nasaslvt/project-owl/doc/failure-analysis/5V_transient.png

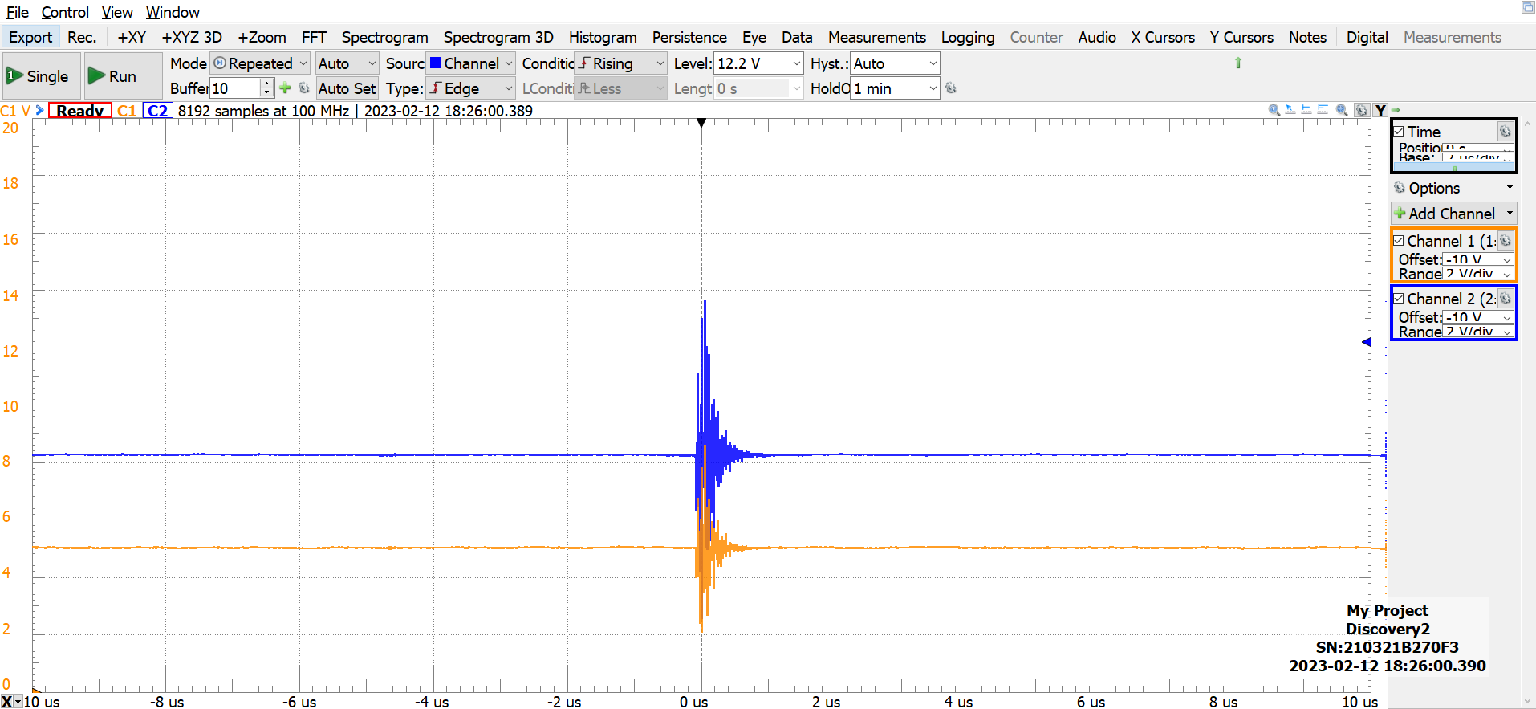
doc/failure-analysis/5V_transient.png
