nasaslvt/project-owl/doc/failure-analysis/Ground_bounce.png

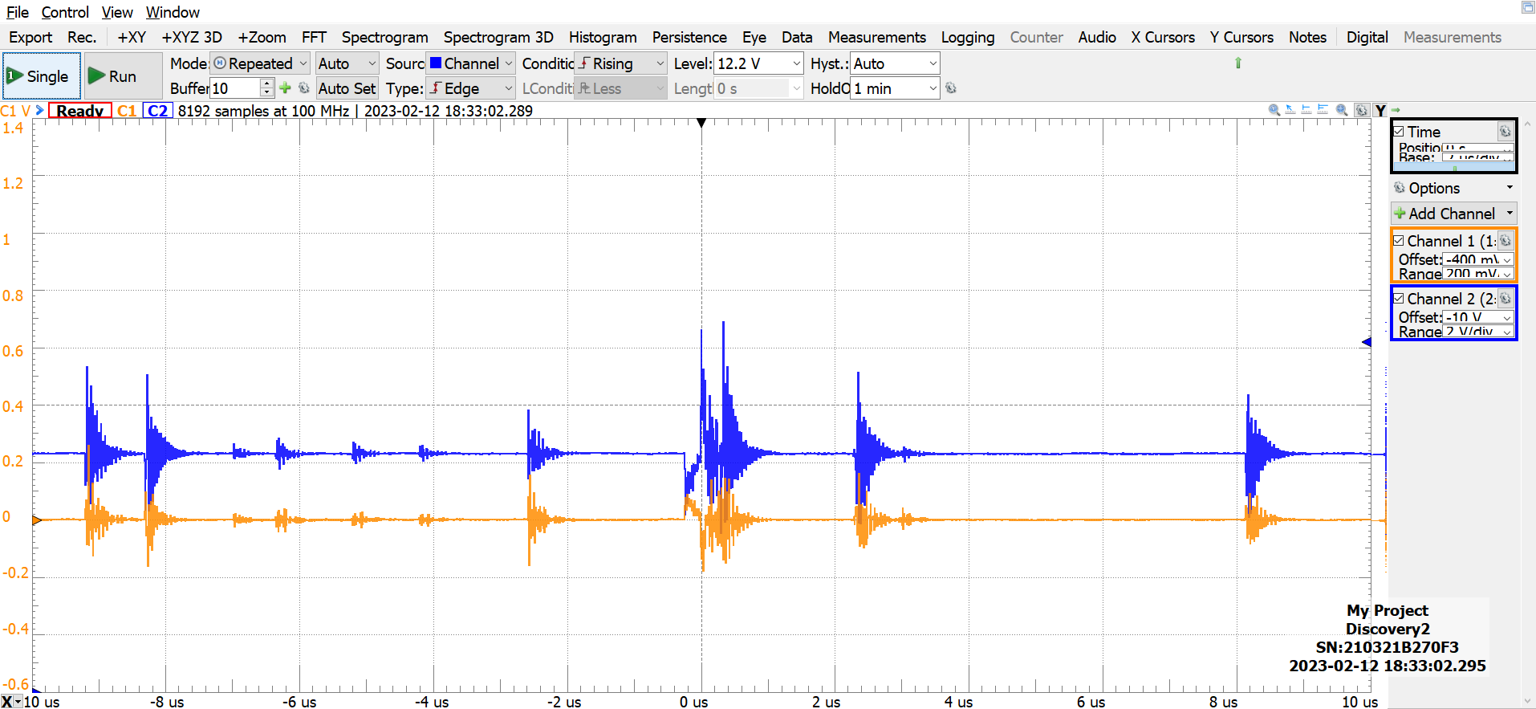
doc/failure-analysis/Ground_bounce.png
