nasaslvt/project-owl/doc/failure-analysis/PWM_kickback.png

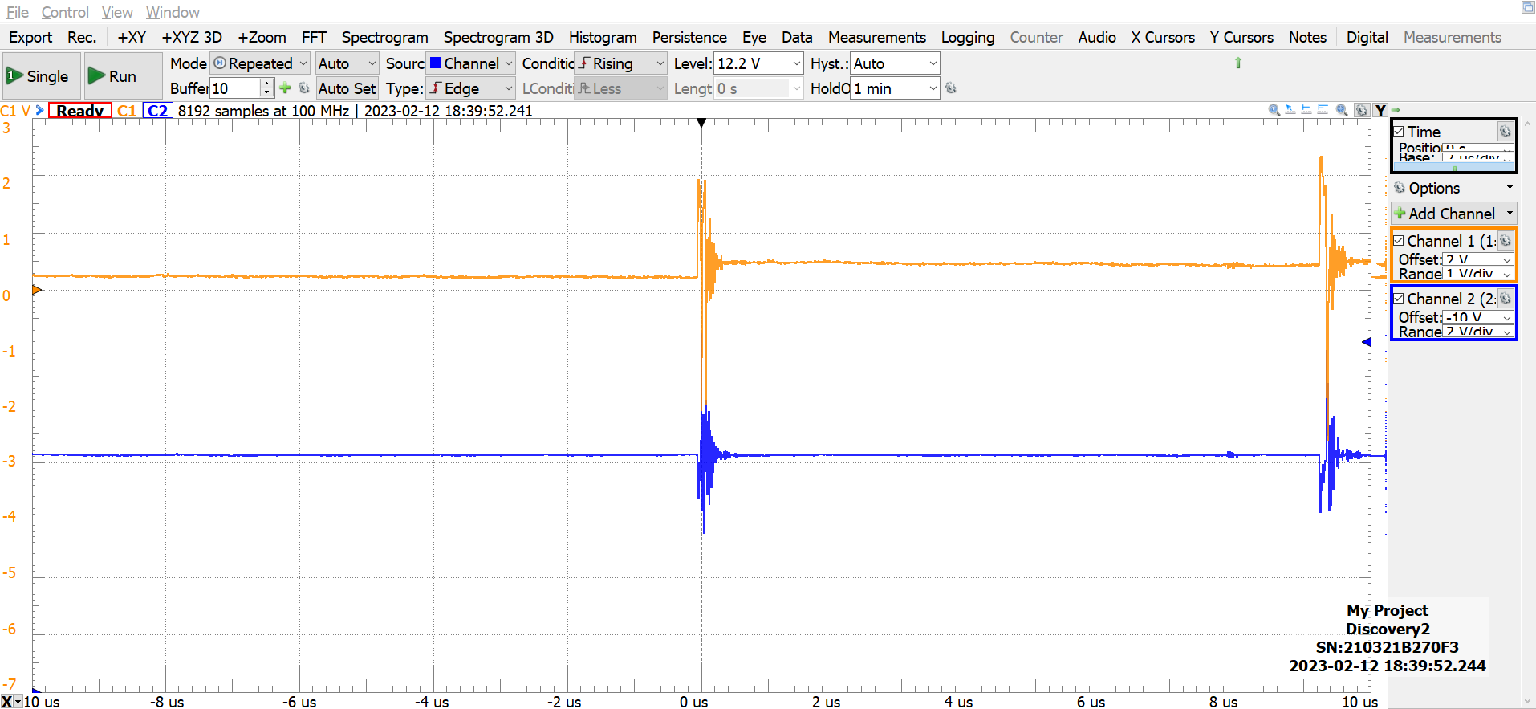
doc/failure-analysis/PWM_kickback.png
