nasaslvt/project-owl/doc/failure-analysis/Servo_startup.png

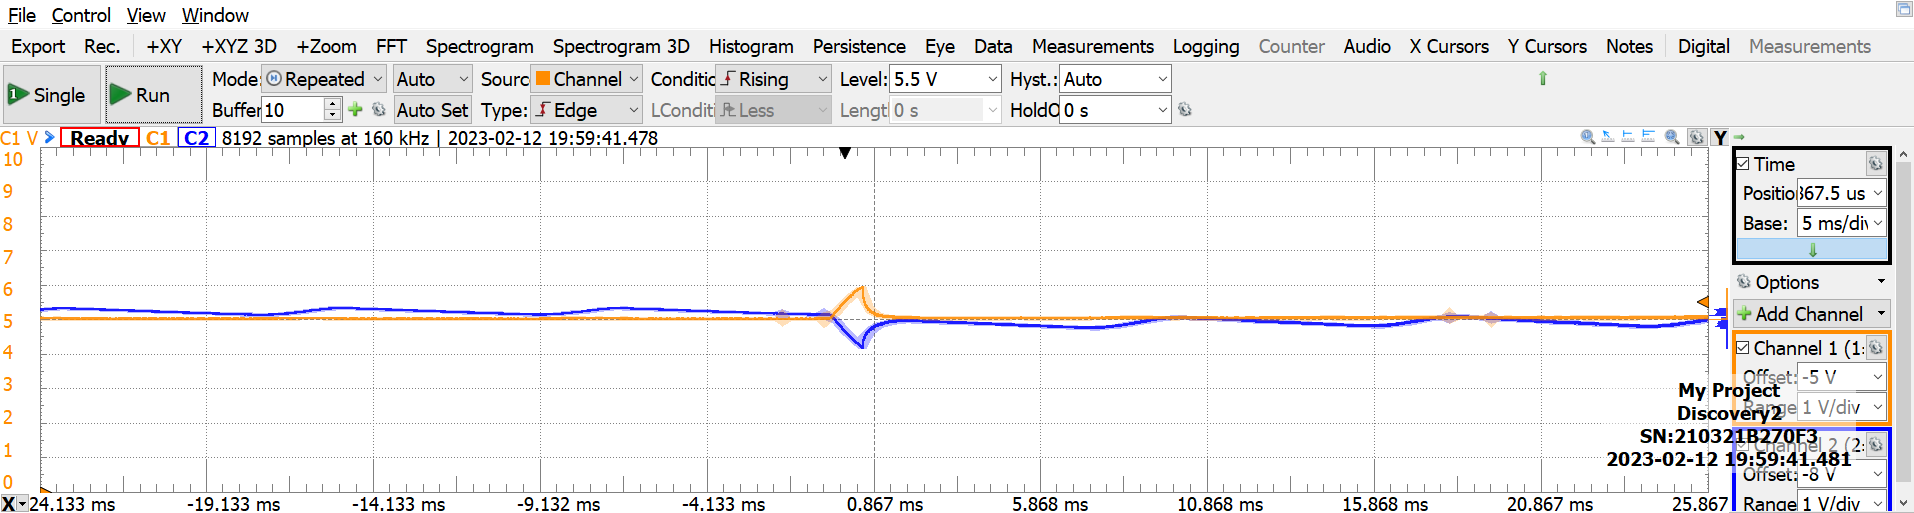
doc/failure-analysis/Servo_startup.png
