nasaslvt/project-owl/doc/Old/cape_route_v1-2.pdf

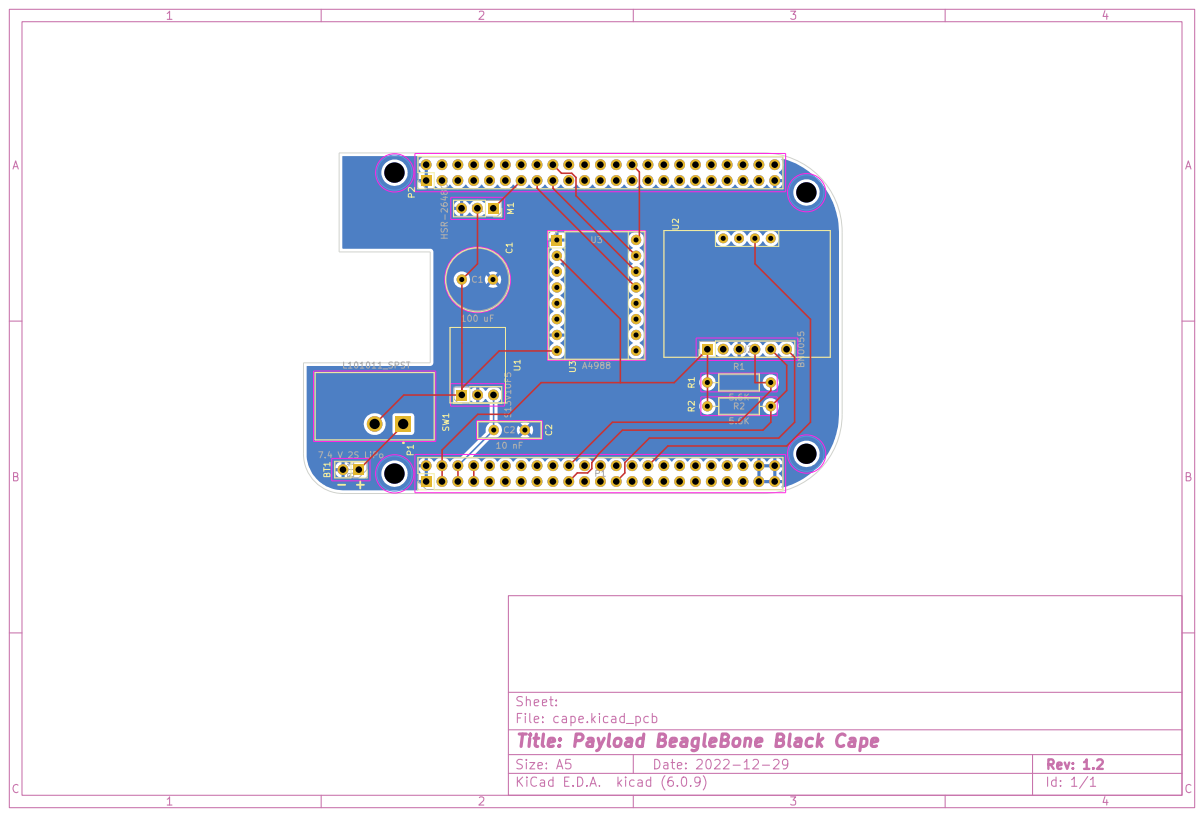
[picture p22: page 1]
