nasaslvt/project-owl/doc/Old/cape_route_v1-1.pdf

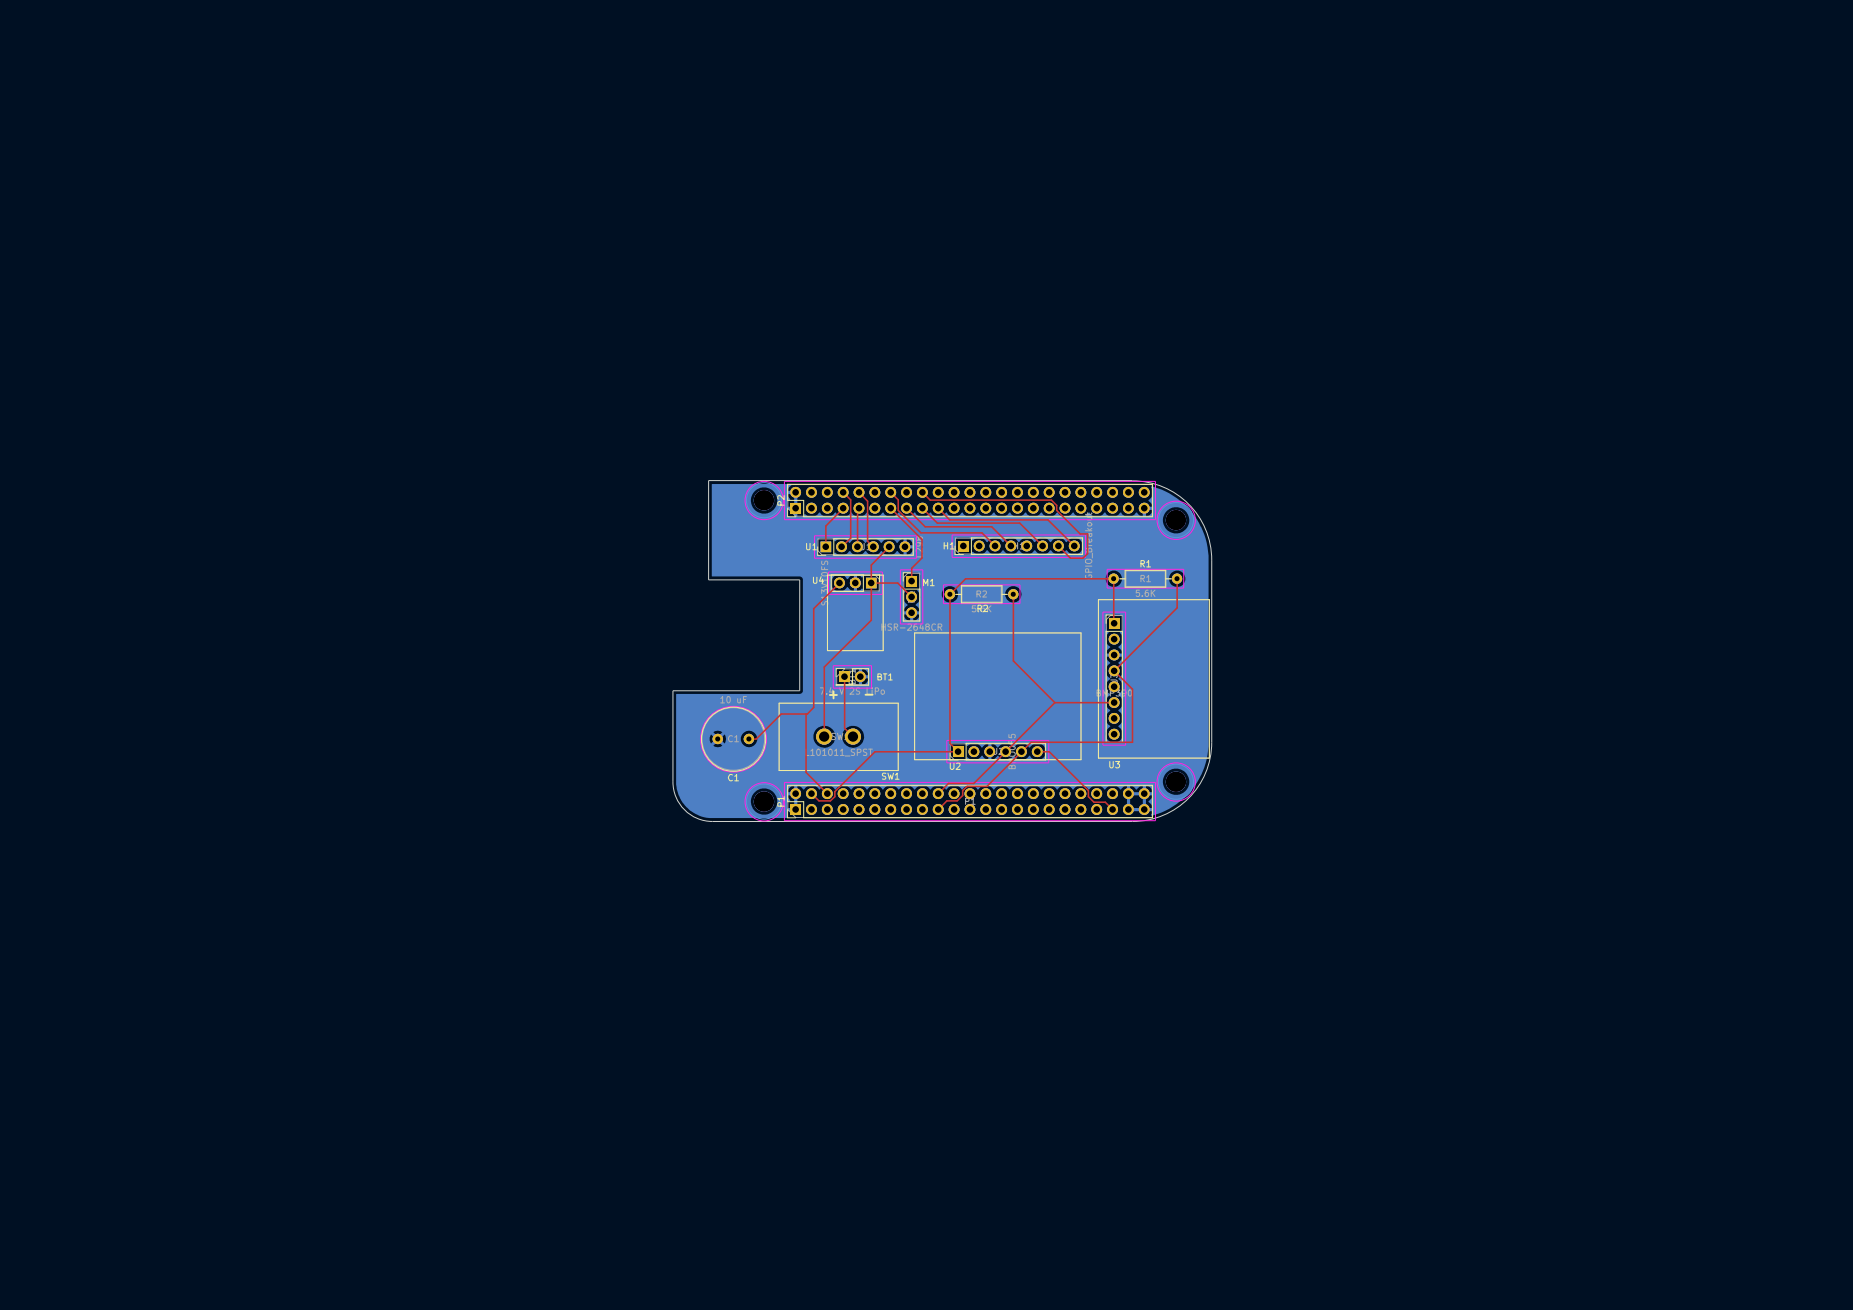
[picture p23: page 1]
