nasaslvt/project-owl/doc/Old/cam_v1-1.pdf

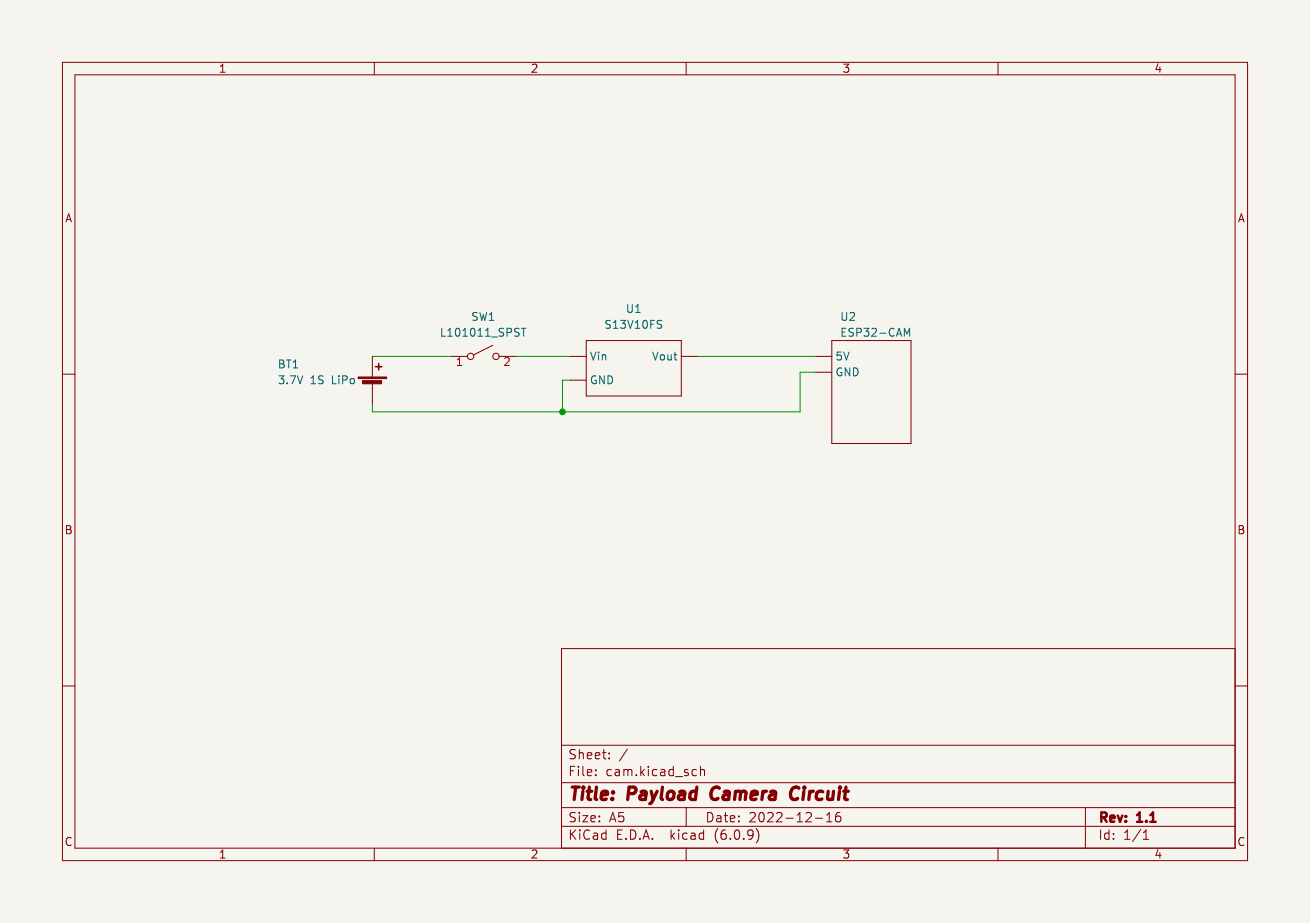
[picture p24: page 1]
