nasaslvt/project-owl/doc/Old/main_v1-4.pdf

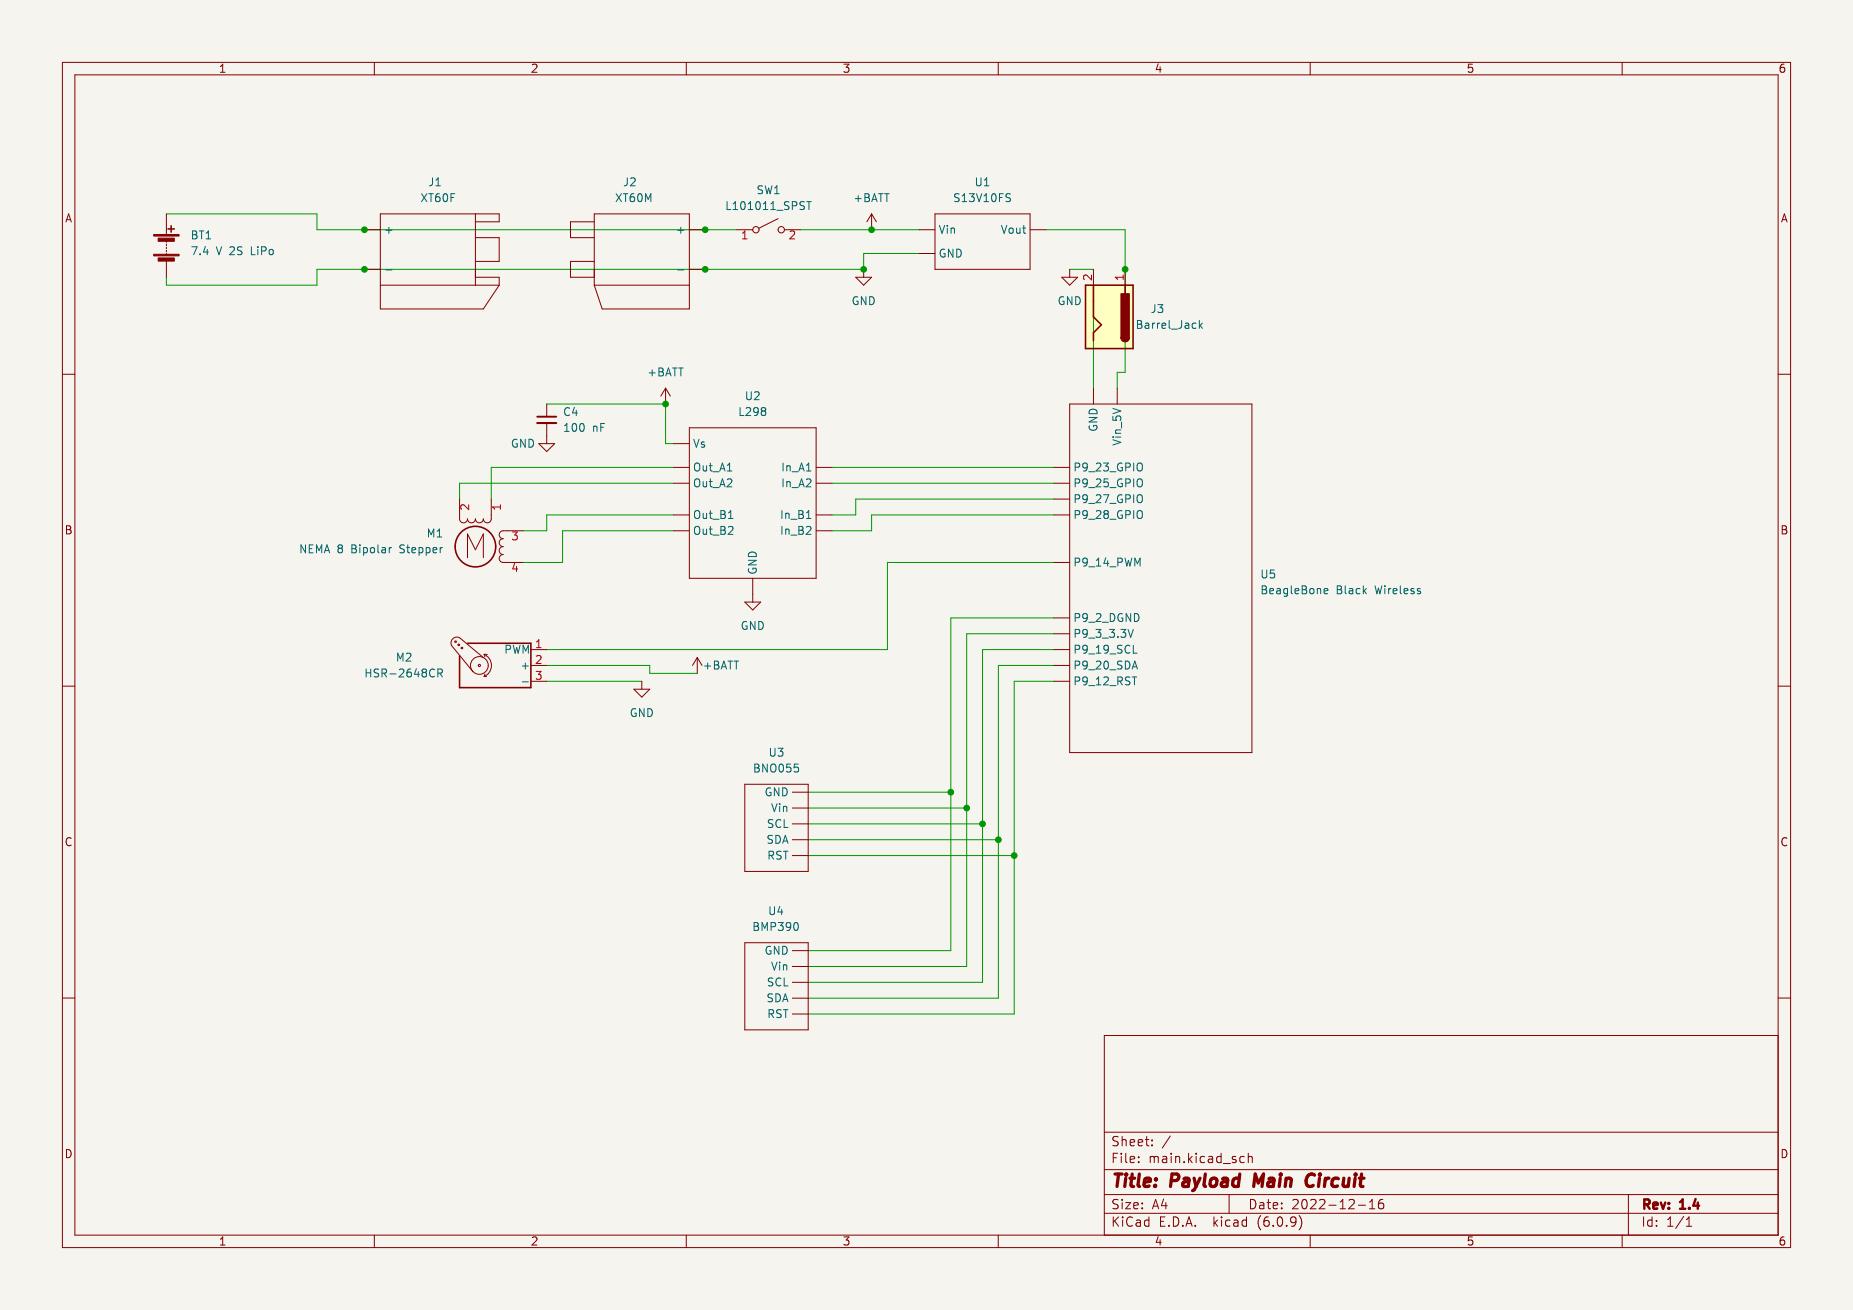
[picture p25: page 1]
