nasaslvt/project-owl/doc/Old/cam_v1-0.pdf

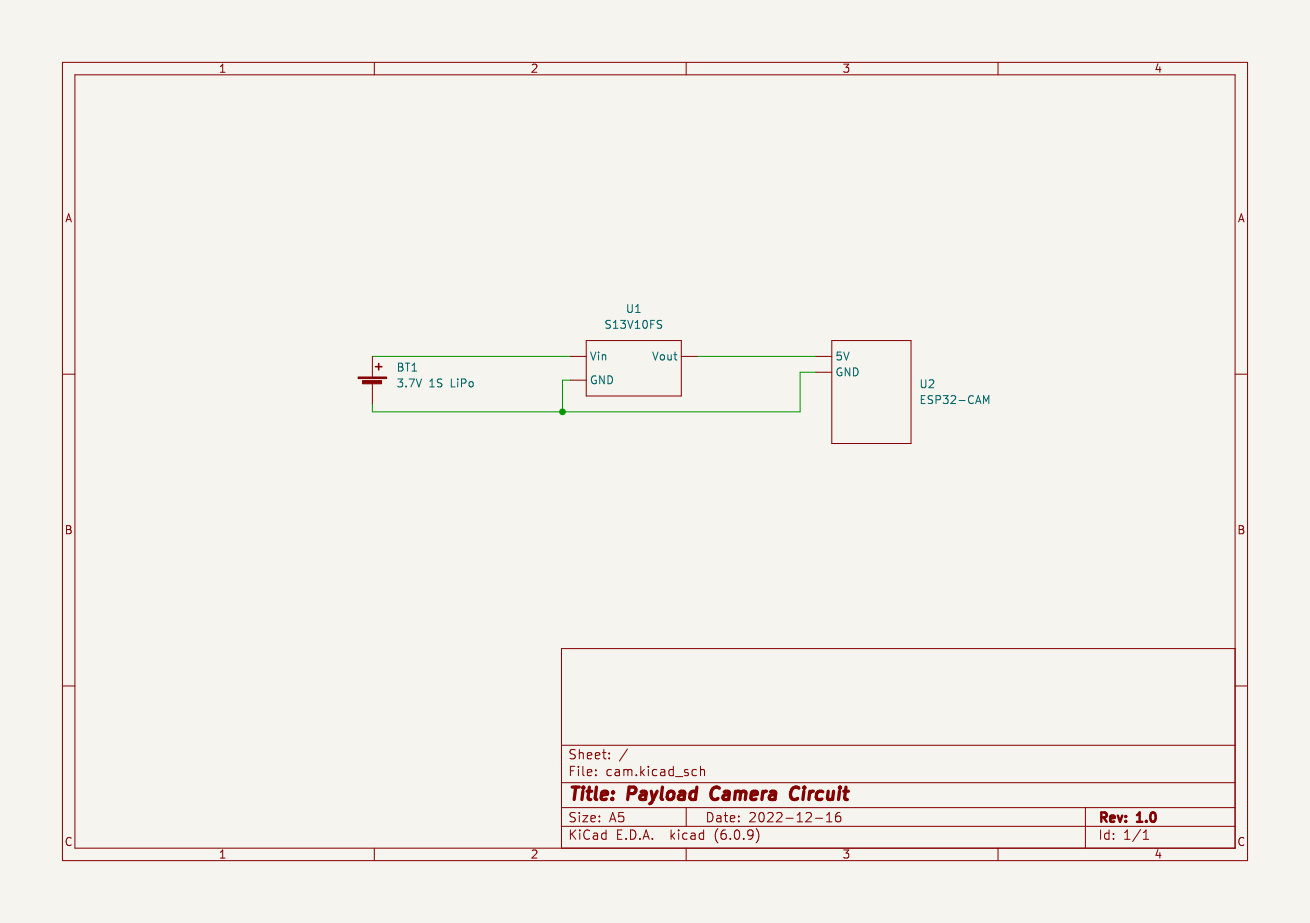
[picture p26: page 1]
