nasaslvt/project-owl/doc/Old/main_v1-3.pdf

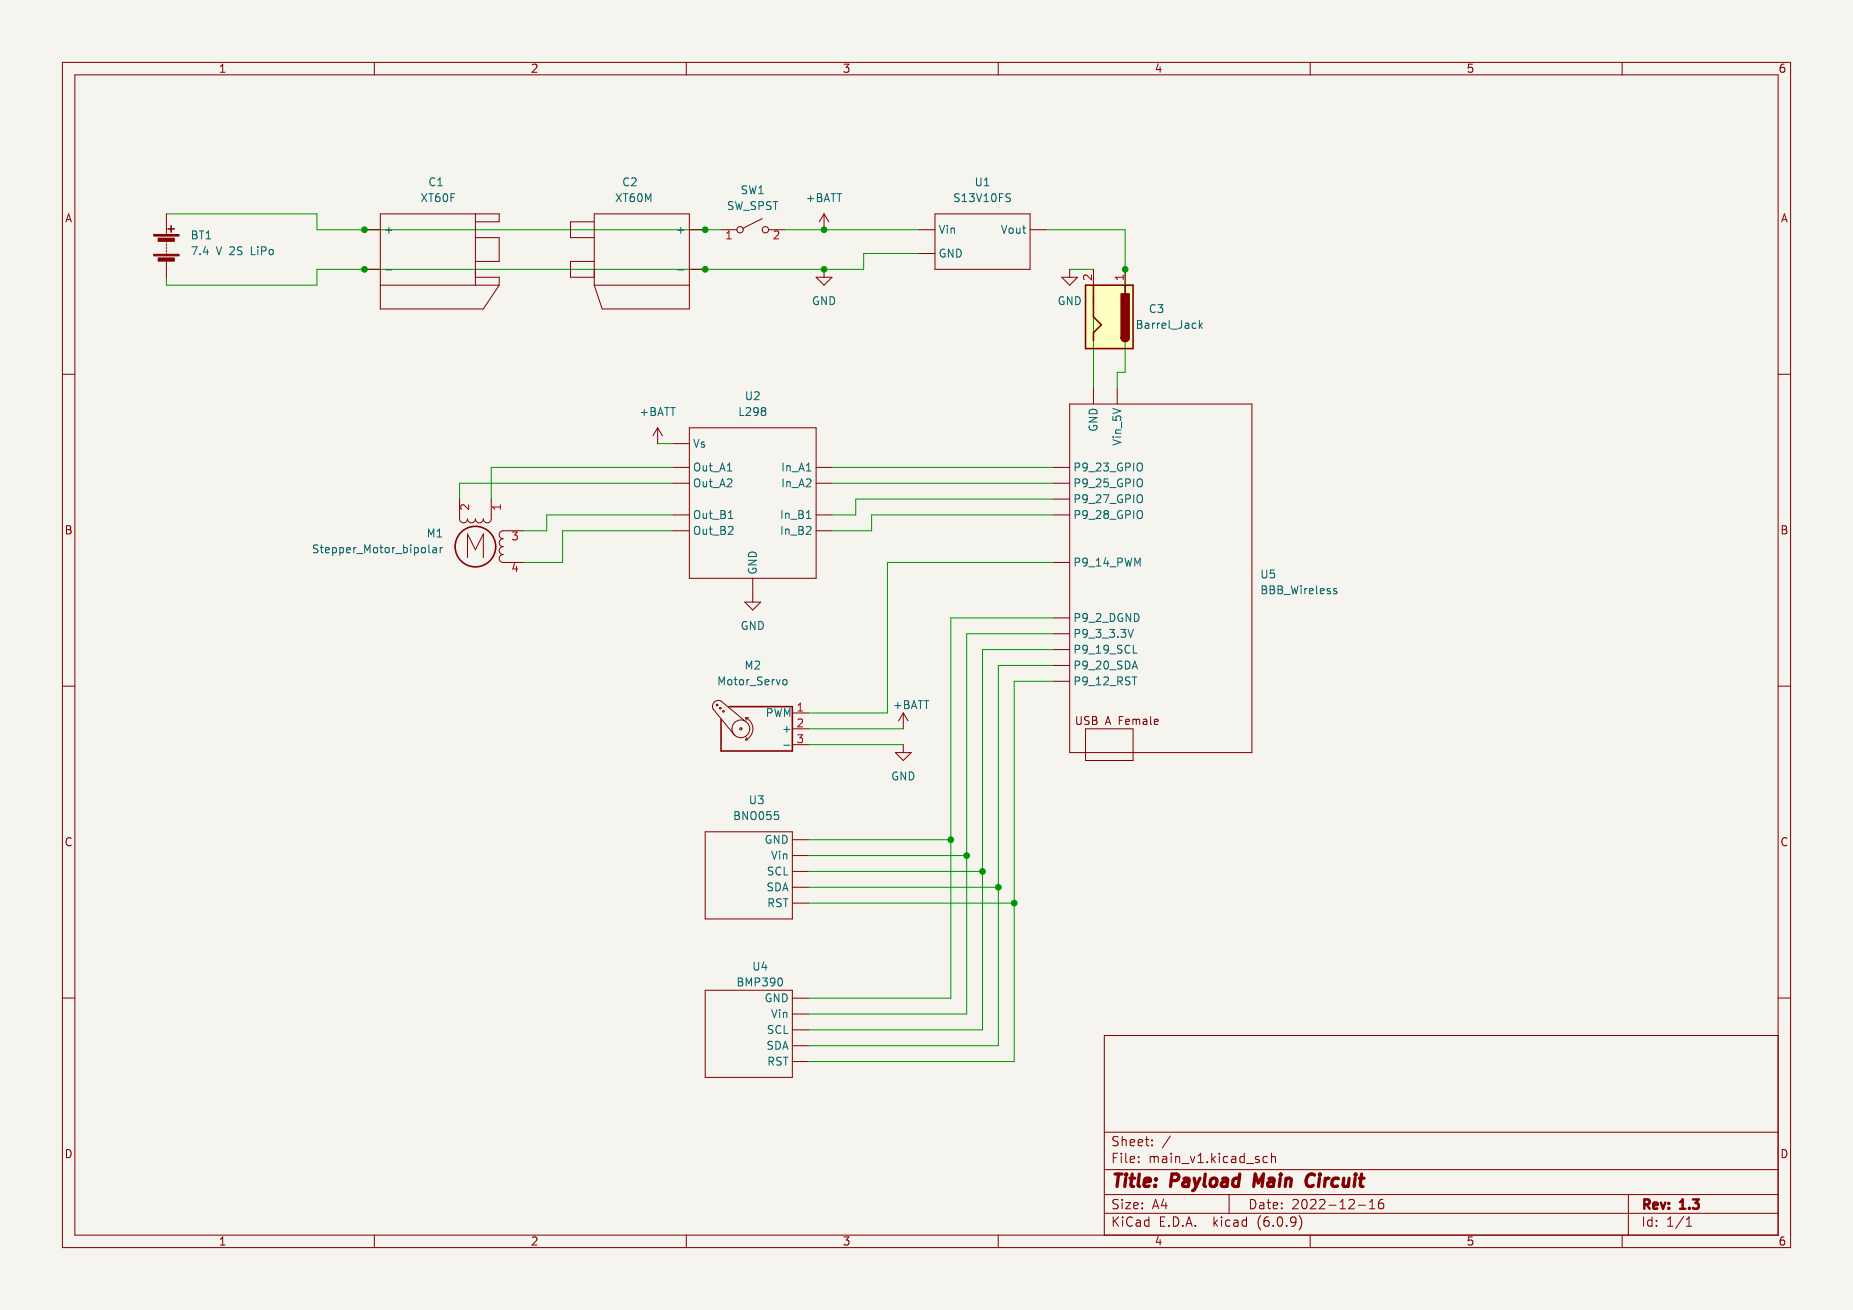
[picture p27: page 1]
