nasaslvt/project-owl/doc/Old/main_v1-2.pdf

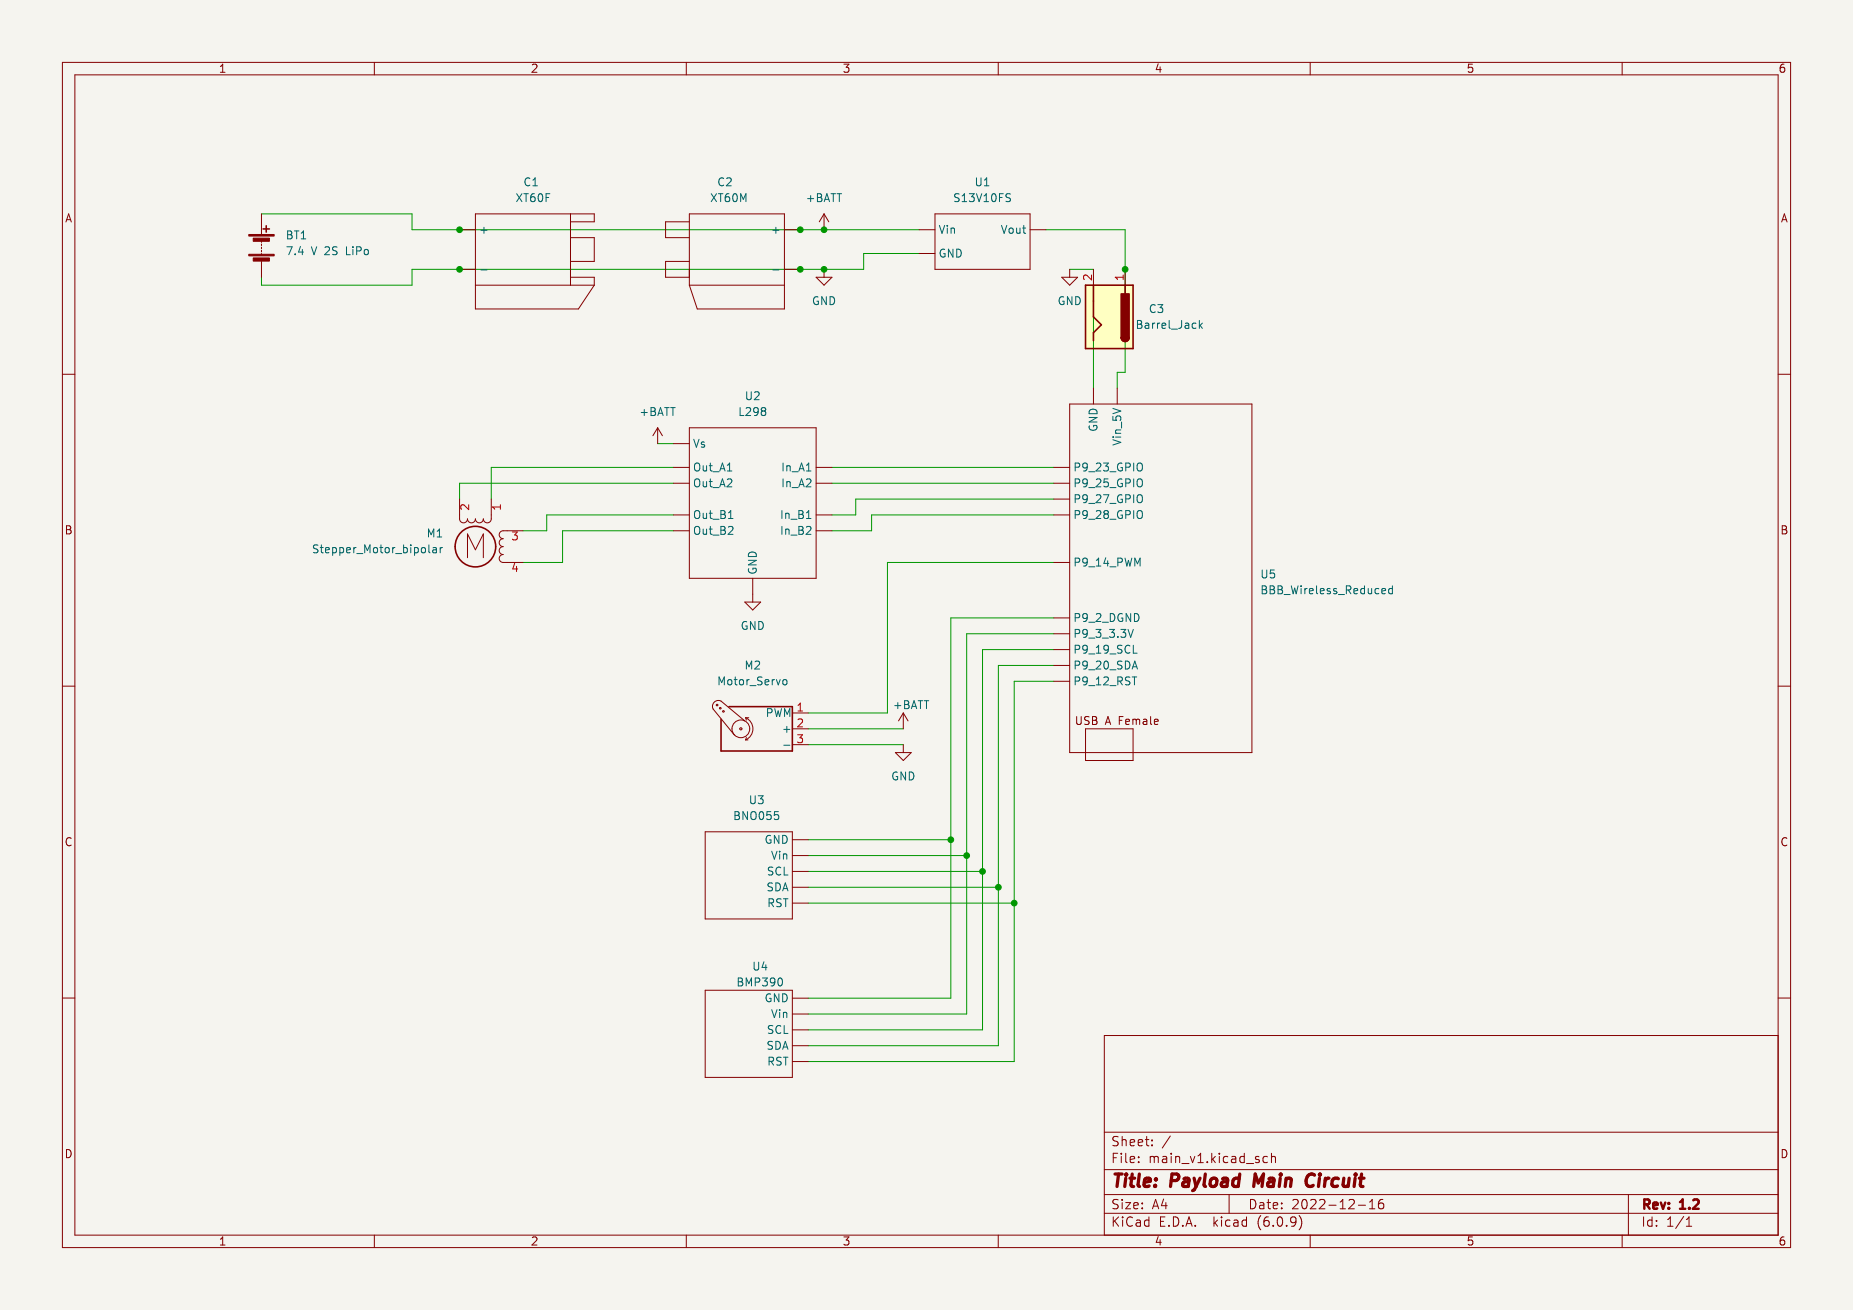
[picture p28: page 1]
