nasaslvt/project-owl/doc/Old/main_v1-1.pdf

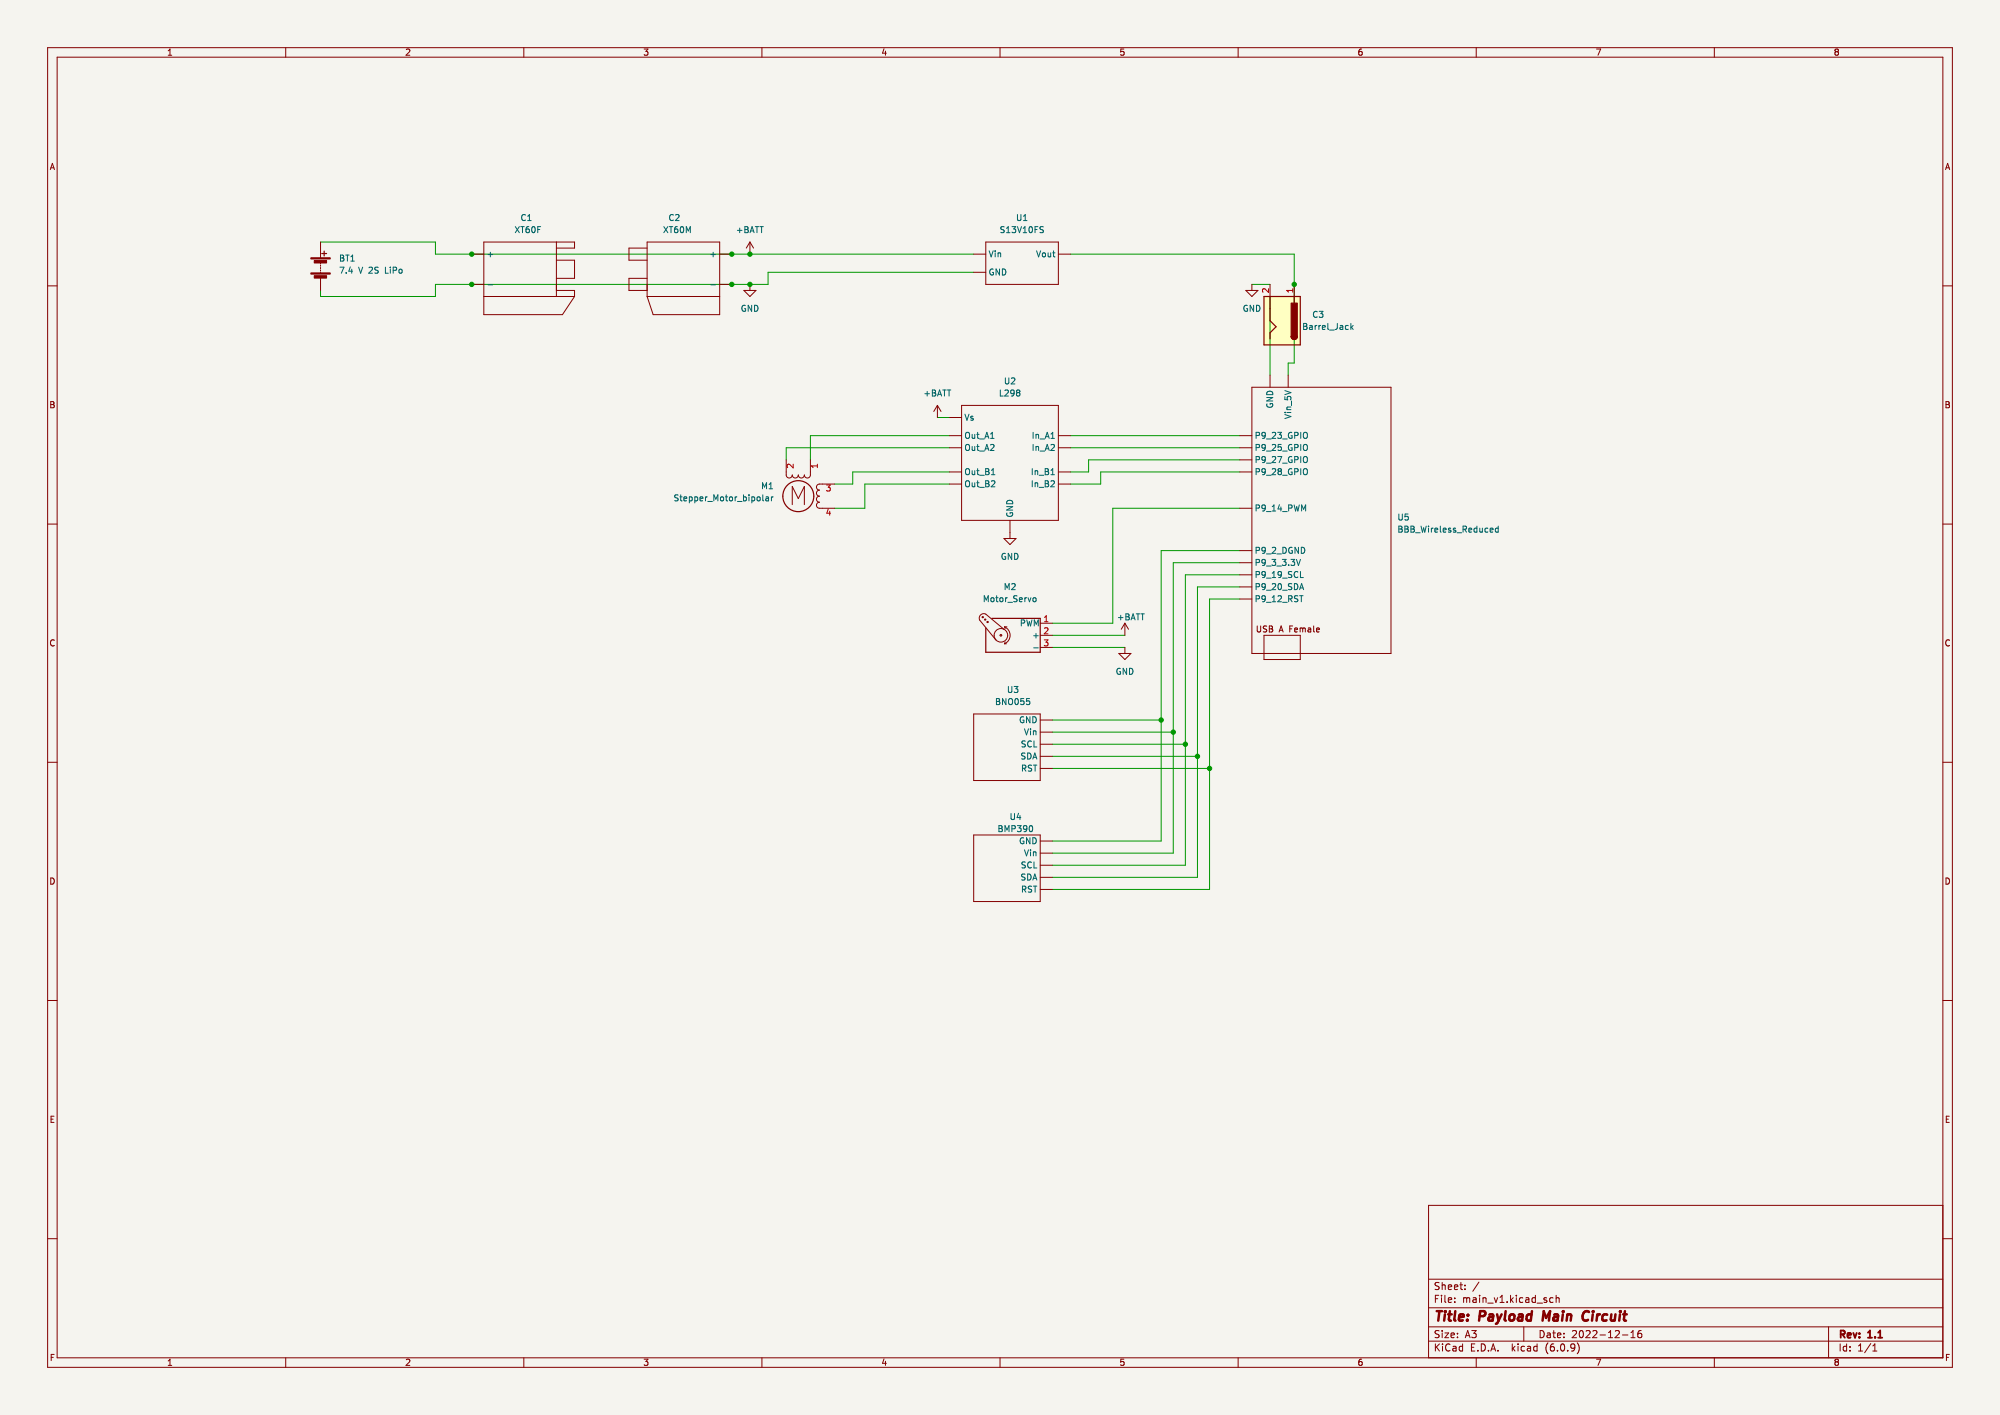
[picture p29: page 1]
