nasaslvt/project-owl/doc/Old/main_v1-0.pdf

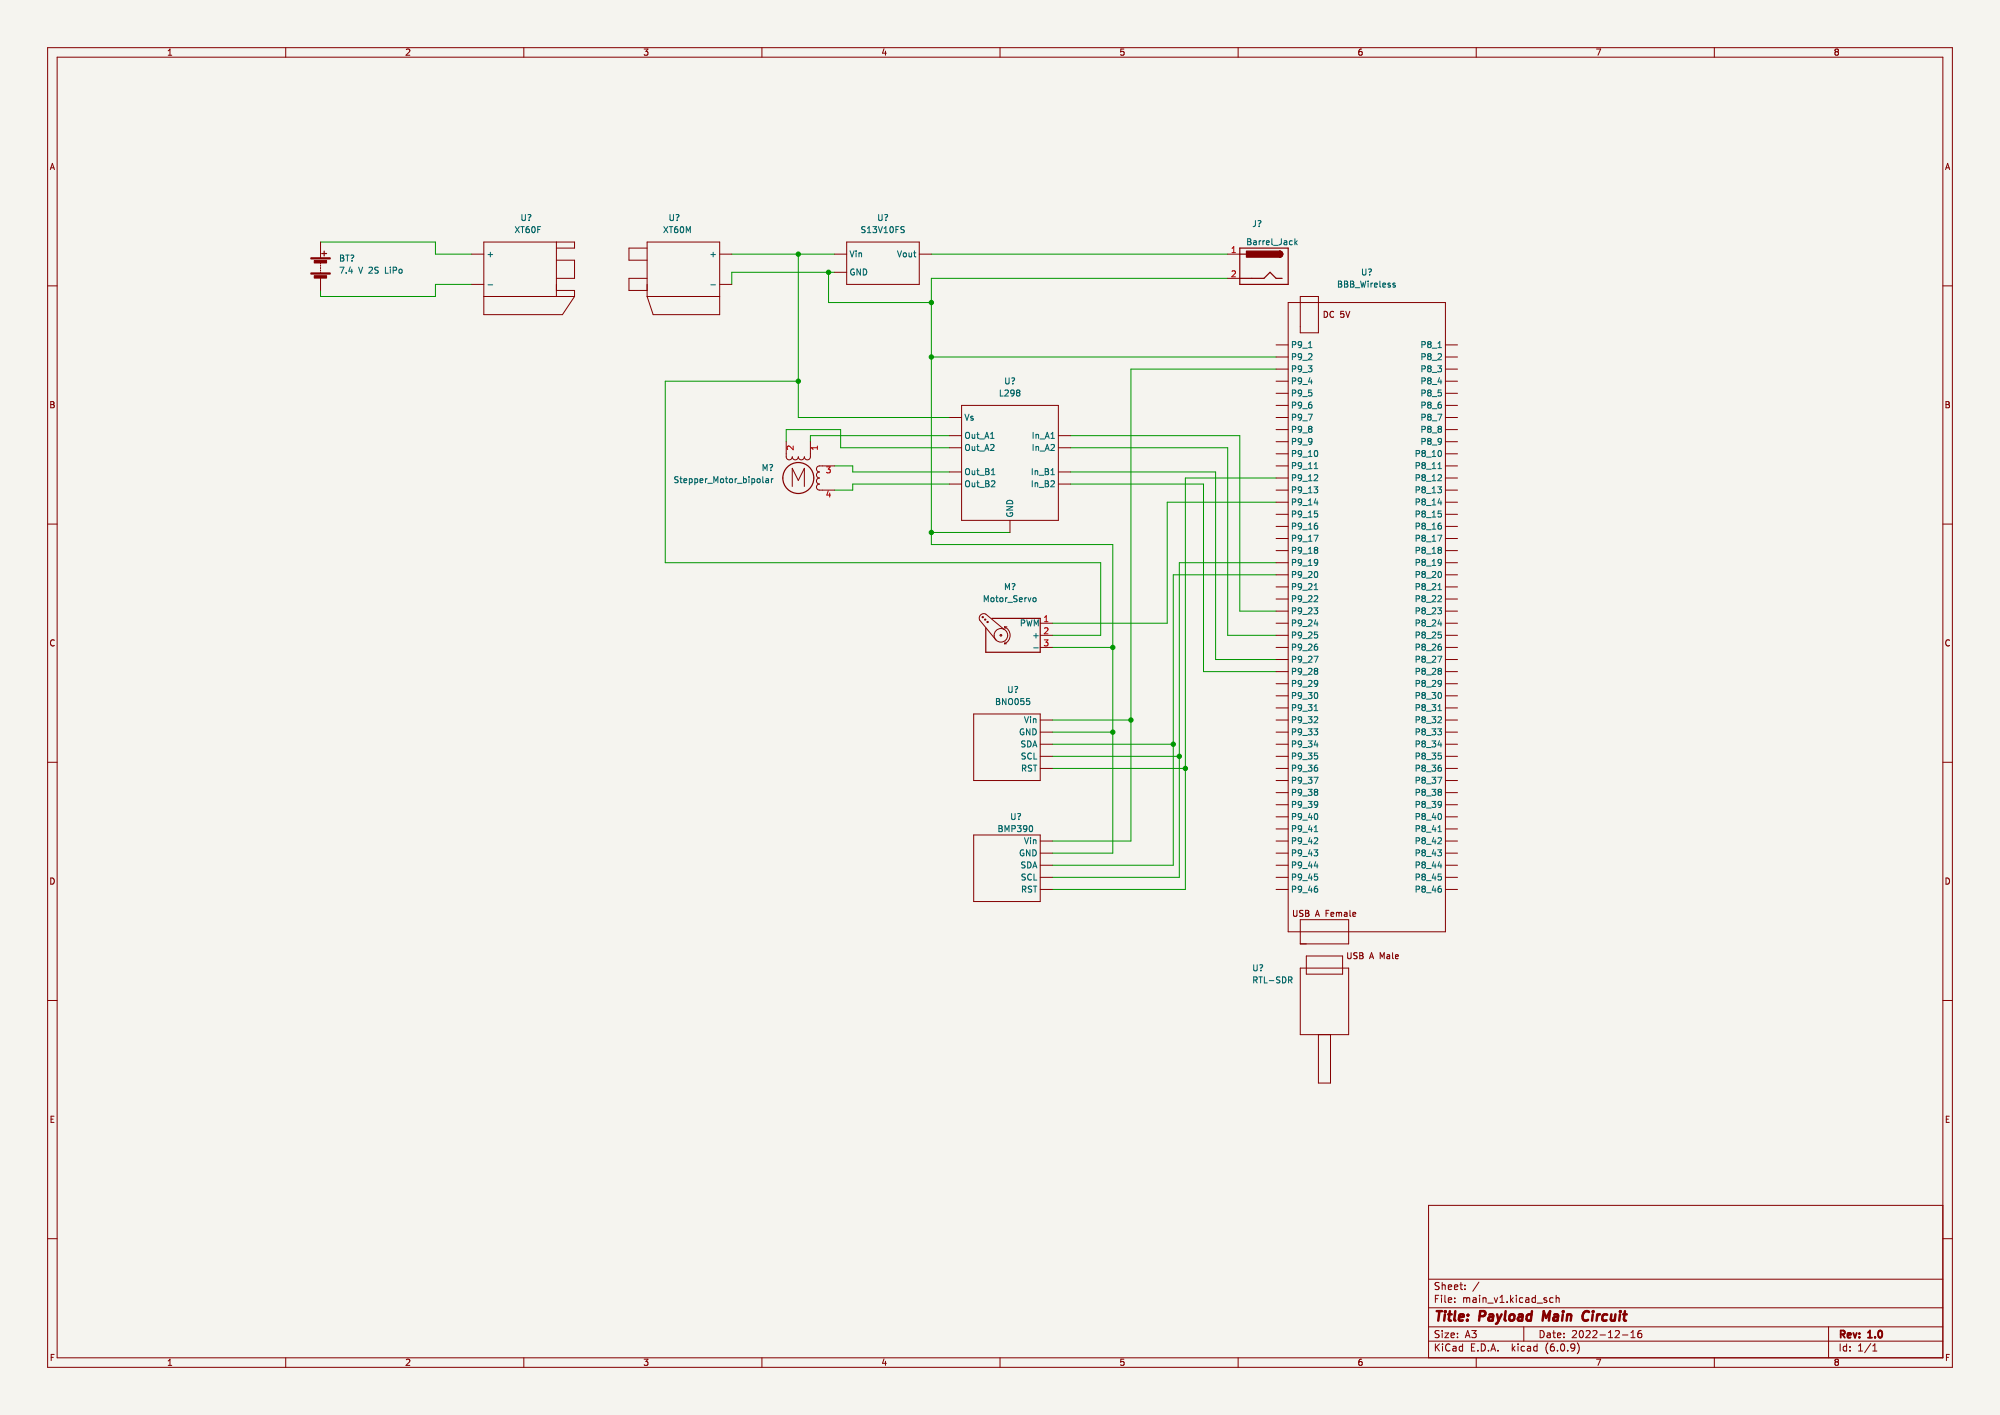
[picture p30: page 1]
