nasaslvt/project-owl/schematic/main_v1.kicad_sch

## KiCad design schematic/main_v1.kicad_sch (2022-12-16)

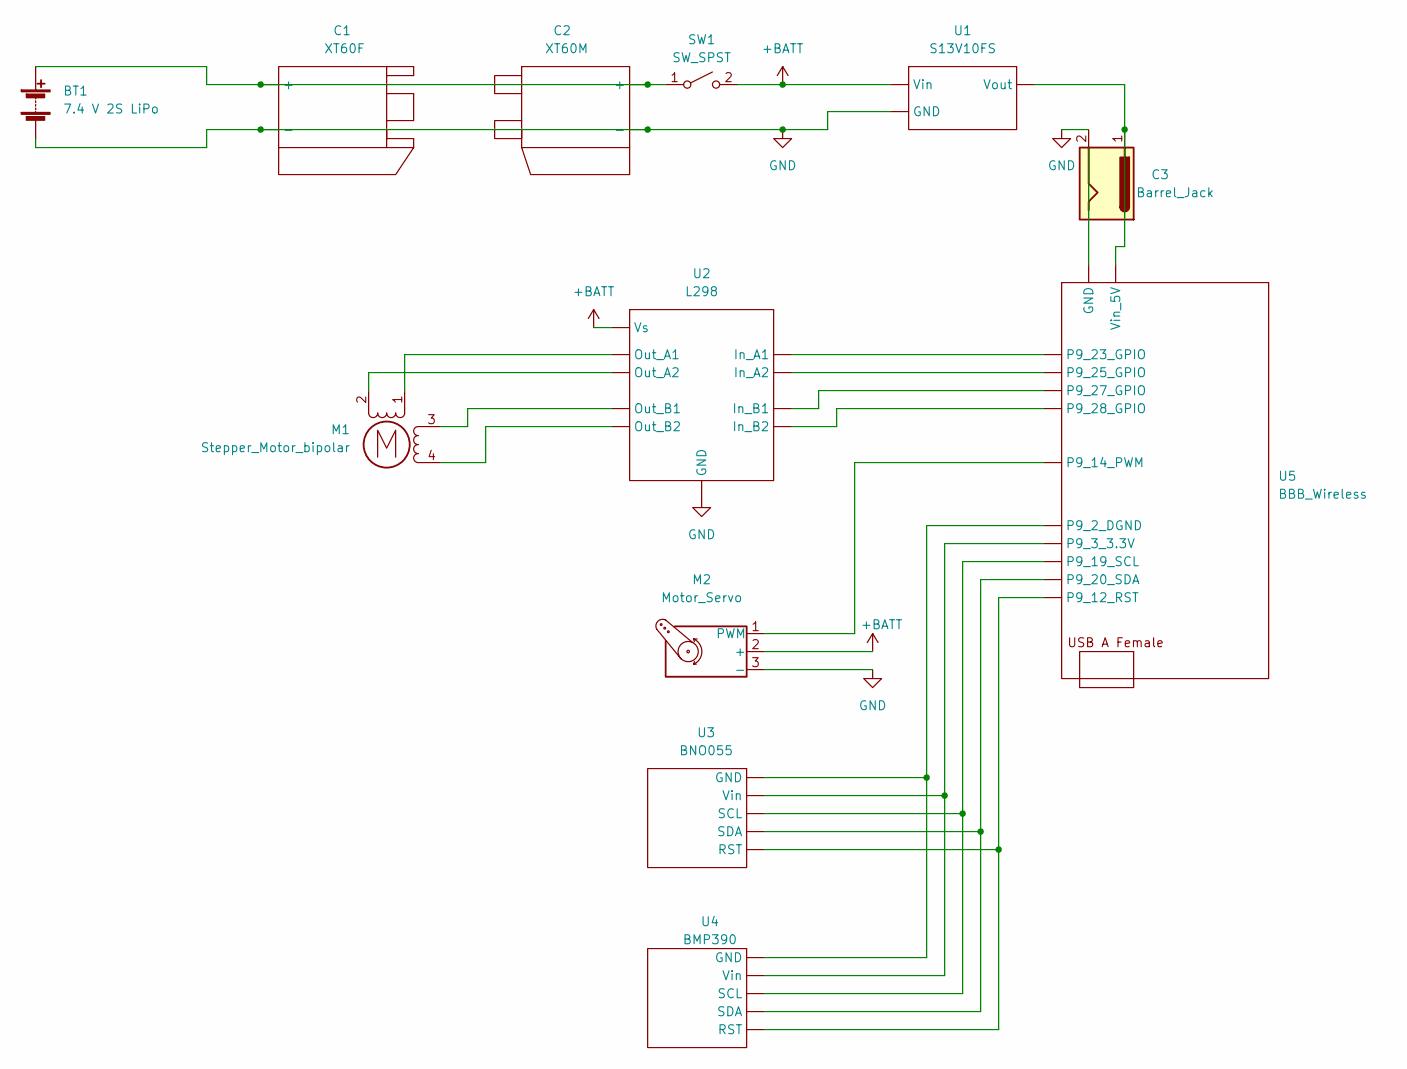
[picture p35: schematic main_v1.kicad_sch]

Parts:
BT1: 7.4 V 2S LiPo
C1: XT60F
C2: XT60M
C3: Barrel_Jack
M1: Stepper_Motor_bipolar
M2: Motor_Servo
SW1: SW_SPST
U1: S13V10FS
U2: L298
U3: BNO055
U4: BMP390
U5: BBB_Wireless

Connections:
+BATT: M2.2 (+), SW1.2 (B), U1., U2.
GND: BT1.2 (-), C1., C2., C3.2, M2.3 (-), U1., U2.
unnamed: BT1.1 (+), C1., C2., SW1.1 (A)
unnamed: C3.1, U1., U5.
unnamed: M1.1, U2.
unnamed: M1.2 (-), U2.
unnamed: M1.3, U2.
unnamed: M1.4, U2.
unnamed: M2.1 (PWM), U5.
unnamed: U2., U5.
unnamed: U3., U4., U5.
